OLIMEX/STMP1-A13-EVB/HARDWARE/STMP1(A13)-SOM-EVB-Rev-B/3d/USBB1-FRWH-4A(USB-Ax2)---CUI_DEVICES_UJ2-ADH-1-TH.step

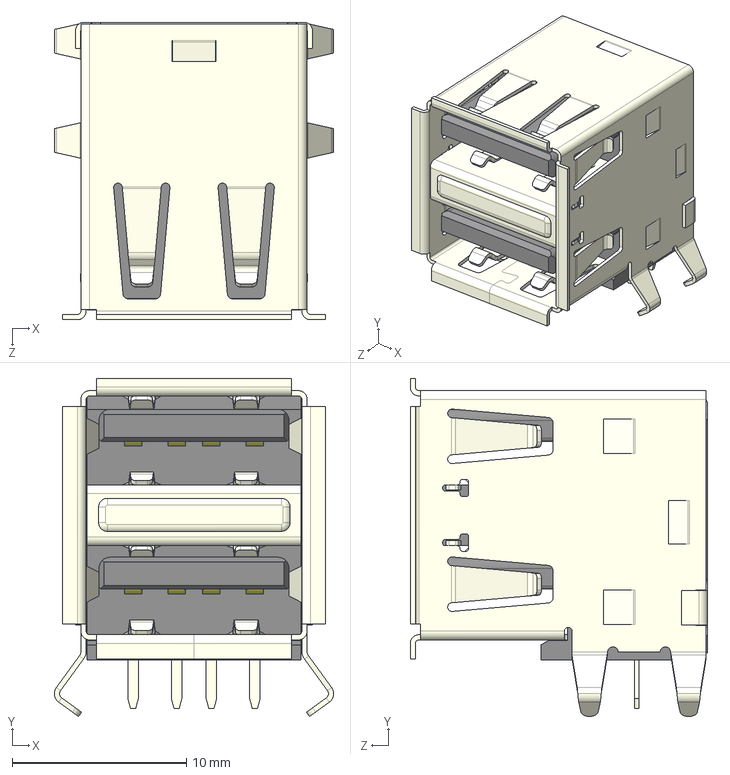
[picture p20: CAD file, 2021-05-21]
HARDWARE/STMP1(A13)-SOM-EVB-Rev-B/3d/USBB1-FRWH-4A(USB-Ax2)---CUI_DEVICES_UJ2-ADH-1-TH.step
16.0 x 19.4 x 17.1 mm
