OLIMEX/STMP1-A13-EVB/HARDWARE/STMP1(A13)-SOM-EVB-Rev-B/3d/SO-8_150mil---SN65HVDA1050AQDRQ1.STEP

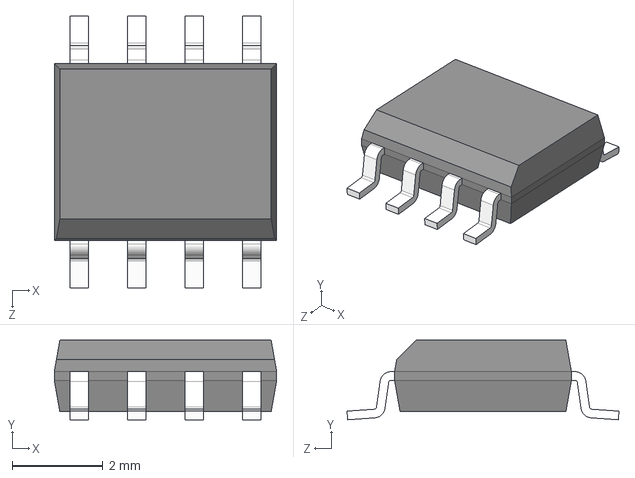
[picture p22: CAD file, 2021-05-21]
HARDWARE/STMP1(A13)-SOM-EVB-Rev-B/3d/SO-8_150mil---SN65HVDA1050AQDRQ1.STEP
4.90 x 1.75 x 5.99 mm
