OLIMEX/STMP1-A13-EVB/HARDWARE/STMP1(A13)-SOM-EVB-Rev-B/3d/DO-214AA_SMB.step

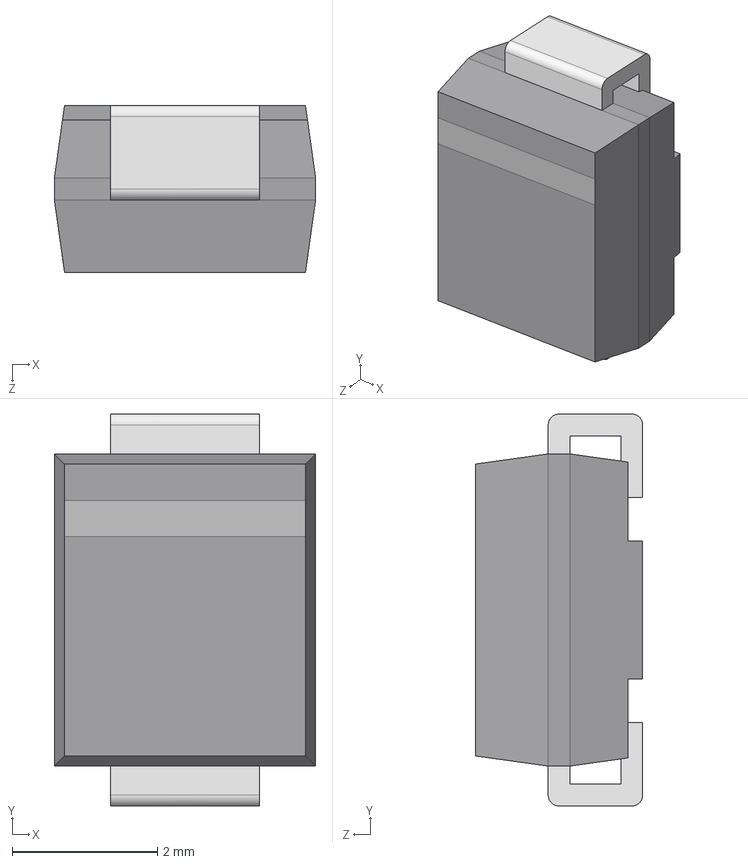
[picture p23: CAD file, 2021-05-21]
HARDWARE/STMP1(A13)-SOM-EVB-Rev-B/3d/DO-214AA_SMB.step
3.60 x 5.40 x 2.30 mm
