OLIMEX/STMP1-A13-EVB/HARDWARE/STMP1(A13)-SOM-EVB-Rev-B/3d/SOT-23-5.step

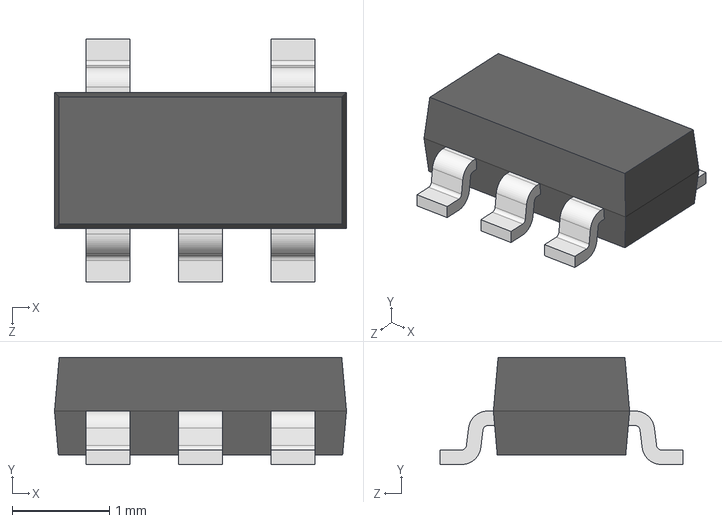
[picture p24: CAD file, 2021-05-21]
HARDWARE/STMP1(A13)-SOM-EVB-Rev-B/3d/SOT-23-5.step
3.00 x 1.10 x 2.50 mm
