OLIMEX/STMP1-A13-EVB/HARDWARE/STMP1(A13)-SOM-EVB-Rev-B/3d/U_FL-R-SMT-1.step

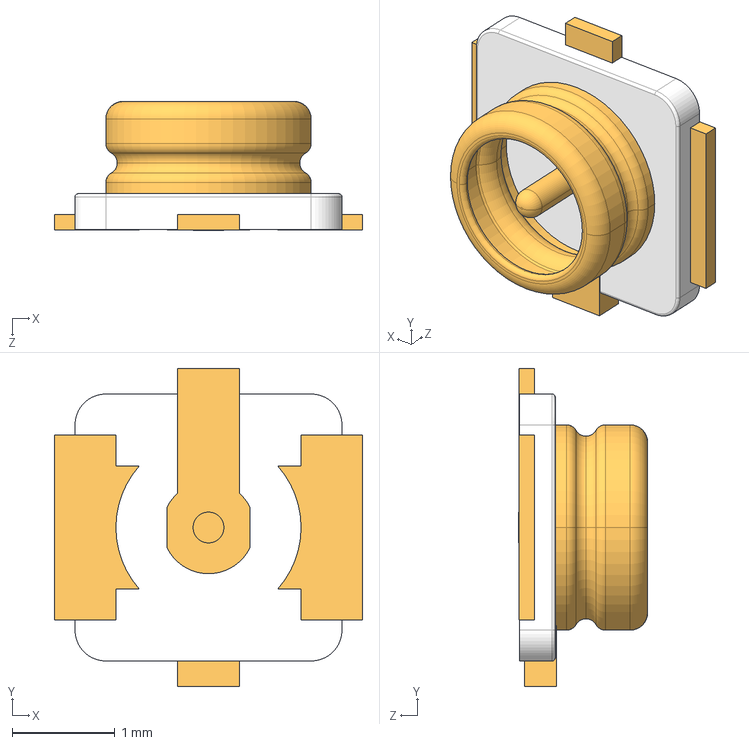
[picture p25: CAD file, 2021-05-21]
HARDWARE/STMP1(A13)-SOM-EVB-Rev-B/3d/U_FL-R-SMT-1.step
3.00 x 3.10 x 1.26 mm
